edmundsj/MCP3561DevBoard/data/MCP3561DevBoard~run_type-test~replicate-0~amplitude-0.1~frequency-105.csv

{'sampling_frequency': 9760 | 'n_samples': 1000}
Time (s) | Voltage (mV) | Sync
0.0 | 390.7336950302124 | 0
0.00010245901639344262 | 352.47015953063965 | 0
0.00020491803278688525 | 317.92298555374146 | 0
0.00030737704918032784 | 287.1094822883606 | 0
0.0004098360655737705 | 260.1095080375671 | 0
0.0005122950819672131 | 237.3483180999756 | 0
0.0006147540983606557 | 218.682324886322 | 0
0.0007172131147540983 | 204.36408519744873 | 0
0.000819672131147541 | 194.43097114562988 | 0
0.0009221311475409836 | 188.91327381134033 | 0
0.0010245901639344263 | 187.7197265625 | 0
0.001127049180327869 | 190.85032939910886 | 0
0.0012295081967213114 | 198.3275055885315 | 0
0.001331967213114754 | 210.37942171096802 | 0
0.0014344262295081967 | 226.81213617324826 | 0
0.0015368852459016393 | 247.46317863464353 | 0
0.001639344262295082 | 272.10202217102045 | 0
0.0017418032786885246 | 300.724732875824 | 0
0.0018442622950819673 | 333.5036158561706 | 0
0.00194672131147541 | 369.79901790618896 | 0
0.0020491803278688526 | 409.8544478416443 | 0
0.002151639344262295 | 453.3386707305908 | 0
0.002254098360655738 | 499.9633312225342 | 0
0.0023565573770491805 | 549.453842639923 | 0
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
