edmundsj/MCP3561DevBoard/data/MCP3561DevBoard~run_type-test~replicate-0~amplitude-0.1~frequency-205.csv

{'sampling_frequency': 9760 | 'n_samples': 1000}
Time (s) | Voltage (mV) | Sync
0.0 | 2002.4611115455627 | 0
0.00010245901639344262 | 1933.1338763236997 | 0
0.00020491803278688525 | 1850.1111388206482 | 0
0.00030737704918032784 | 1755.0345182418823 | 0
0.0004098360655737705 | 1649.6632575988767 | 0
0.0005122950819672131 | 1535.803413391113 | 0
0.0006147540983606557 | 1415.305495262146 | 0
0.0007172131147540983 | 1290.2493596076965 | 0
0.000819672131147541 | 1162.9807949066162 | 0
0.0009221311475409836 | 1035.5580210685728 | 0
0.0010245901639344263 | 910.2926015853882 | 0
0.001127049180327869 | 789.2466902732849 | 0
0.0012295081967213114 | 674.5638728141784 | 0
0.001331967213114754 | 568.4459567070007 | 0
0.0014344262295081967 | 472.3657965660095 | 0
0.0015368852459016393 | 388.2942795753479 | 0
0.001639344262295082 | 317.5370693206787 | 0
0.0017418032786885246 | 261.43680810928345 | 0
0.0018442622950819673 | 220.74172496795651 | 0
0.00194672131147541 | 196.52931690216064 | 0
0.0020491803278688526 | 188.93176317214966 | 0
0.002151639344262295 | 198.02656173706055 | 0
0.002254098360655738 | 223.69648218154904 | 0
0.0023565573770491805 | 265.6956553459167 | 0
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
