edmundsj/MCP3561DevBoard/data/MCP3561DevBoard~run_type-test~replicate-1~amplitude-0.01~frequency-105.csv

{'sampling_frequency': 9760 | 'n_samples': 1000}
Time (s) | Voltage (mV) | Sync
0.0 | 1059.983253479004 | 0
0.00010245901639344262 | 1059.8117351531982 | 0
0.00020491803278688525 | 1060.0454092025757 | 0
0.00030737704918032784 | 1060.715353488922 | 0
0.0004098360655737705 | 1061.8534326553345 | 0
0.0005122950819672131 | 1063.4745955467224 | 0
0.0006147540983606557 | 1065.478527545929 | 0
0.0007172131147540983 | 1067.8746700286865 | 0
0.000819672131147541 | 1070.8561778068542 | 0
0.0009221311475409836 | 1074.0878820419312 | 0
0.0010245901639344263 | 1077.6496410369873 | 0
0.001127049180327869 | 1081.6661596298218 | 0
0.0012295081967213114 | 1085.9855890274048 | 0
0.001331967213114754 | 1090.544593334198 | 0
0.0014344262295081967 | 1095.3872323036194 | 0
0.0015368852459016393 | 1100.7208228111267 | 0
0.001639344262295082 | 1106.3368678092954 | 0
0.0017418032786885246 | 1111.9348168373106 | 0
0.0018442622950819673 | 1117.8203344345093 | 0
0.00194672131147541 | 1124.0154504776 | 0
0.0020491803278688526 | 1130.3435325622556 | 0
0.002151639344262295 | 1136.745572090149 | 0
0.002254098360655738 | 1143.1299090385437 | 0
0.0023565573770491805 | 1149.6920585632324 | 0
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
