edmundsj/MCP3561DevBoard/data/MCP3561DevBoard~run_type-test~replicate-1~amplitude-0.01~frequency-205.csv

{'sampling_frequency': 9760 | 'n_samples': 1000}
Time (s) | Voltage (mV) | Sync
0.0 | 1078.4265875816345 | 0
0.00010245901639344262 | 1071.6858386993408 | 0
0.00020491803278688525 | 1066.3286447525024 | 0
0.00030737704918032784 | 1062.6327395439148 | 0
0.0004098360655737705 | 1060.489547252655 | 0
0.0005122950819672131 | 1059.9482417106626 | 0
0.0006147540983606557 | 1061.091434955597 | 0
0.0007172131147540983 | 1064.0454053878782 | 0
0.000819672131147541 | 1068.5493350028992 | 0
0.0009221311475409836 | 1074.544608592987 | 0
0.0010245901639344263 | 1082.0162773132324 | 0
0.001127049180327869 | 1090.8951044082642 | 0
0.0012295081967213114 | 1100.7703900337217 | 0
0.001331967213114754 | 1111.6401672363281 | 0
0.0014344262295081967 | 1123.294758796692 | 0
0.0015368852459016393 | 1135.5496644973755 | 0
0.001639344262295082 | 1148.1302976608276 | 0
0.0017418032786885246 | 1160.7467293739317 | 0
0.0018442622950819673 | 1173.5087156295776 | 0
0.00194672131147541 | 1186.024832725525 | 0
0.0020491803278688526 | 1197.867465019226 | 0
0.002151639344262295 | 1209.0051412582397 | 0
0.002254098360655738 | 1219.3115830421448 | 0
0.0023565573770491805 | 1228.6534309387207 | 0
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
